danjulio/tCam/tCam-Mini/enclosure/readme.md

## tCam-Mini Enclosures

### 3D printed case
My simple 3D printed enclosure and a GoPro™ compatible mount attachment for both the Rev 2 and Rev 4 PCB tCam-Mini designs, along with the source OpenSCAD program can be found in ```tcam_mini_basic```.

The enclosure is designed to be fastened together using 4 4-40 x 3/8" metal screws (or the M3 equivalent for the rest of the world).

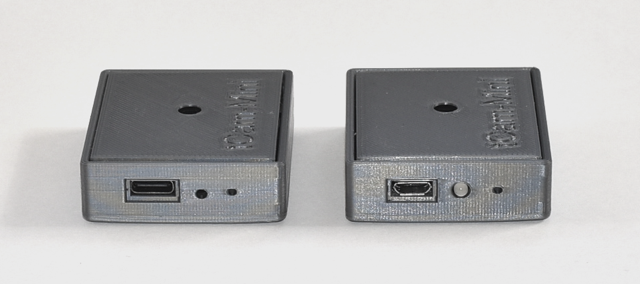
[picture p80: tCam-Mini/enclosure/pictures/tcam_mini_encl_sides.png]
Assembled units for Rev 2 and 4


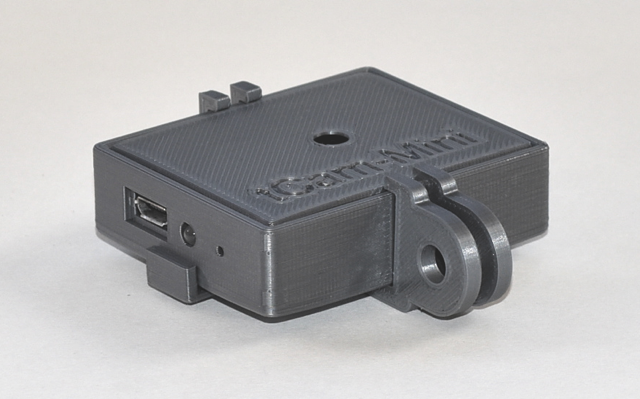
[picture p81: tCam-Mini/enclosure/pictures/tcam_mini_encl_gp_side.png]
Unit with GoPro mount


### Laser cut Front/Rear plates
A super-simple set of drawings suitable for a laser cutter in ```laser``` for a front and rear plate.  Designed to be mounted with plastic stand-offs (~8mm for the front and 5mm for the rear).  Works with either Rev 2 or Rev 4 PCBs.

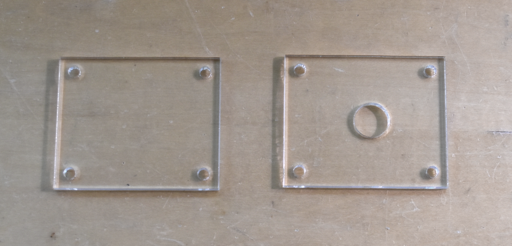
[picture p82: tCam-Mini/enclosure/pictures/tcam_mini_lasercut_pcs.png]
Cut plastic pieces


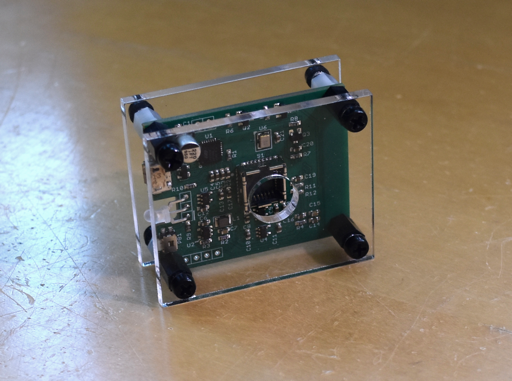
[picture p83: tCam-Mini/enclosure/pictures/tcam_mini_lasercut.png]
Cut plastic assembly


### Zeke Gustafson's 3D printed case
tCam-mini buyer Zeke Gustafson designed a case for the Rev 2 PCB and graciously shared it with me to include here.  His design file and STL files suitable for slicing for a printer can be found in ```zeke_gustafson```.

It is designed to use a 1/4"-20 square nut (McMaster 94855A247) for tripod mounting and 4x #4 thread-forming screws for assembly (McMaster 96068A105).

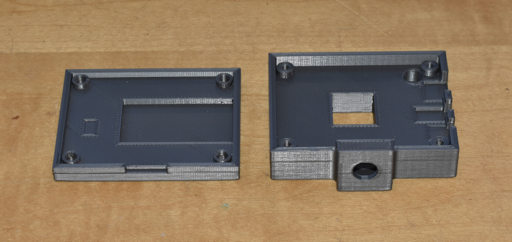
[picture p84: tCam-Mini/enclosure/pictures/zeke_enclosure_pcs.png]
Zeke Gustafson's enclosure pieces


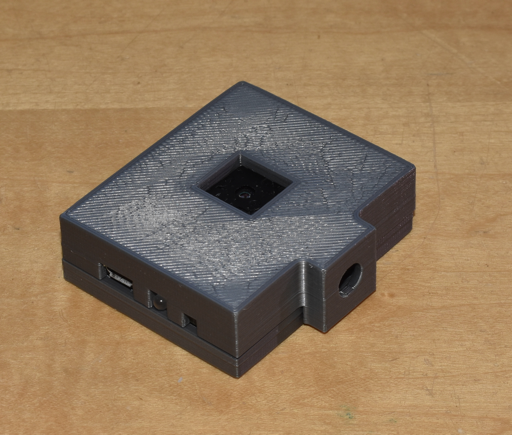
[picture p85: tCam-Mini/enclosure/pictures/zeke_enclosure.png]
Zeke Gustafson's enclosure assembly
