danjulio/tCam/tCam-Eth/hardware/tCam-Eth/documentation/4_layer_pcb_stackup.pdf

## 4-Layer Typical Stackup

Thickness: 1.6mm
Finished Outer Copper: 1oz
Inner Copper: 1oz
Inner layer Residual copper ratio: 70%

Gerber File Identification
Layer 1 Copper (PCB Top): GTL Layer 2 Copper (L2): GL2
Layer 3 Copper (L3): GL3
Layer 4 Copper (PCB Bottom): GBL

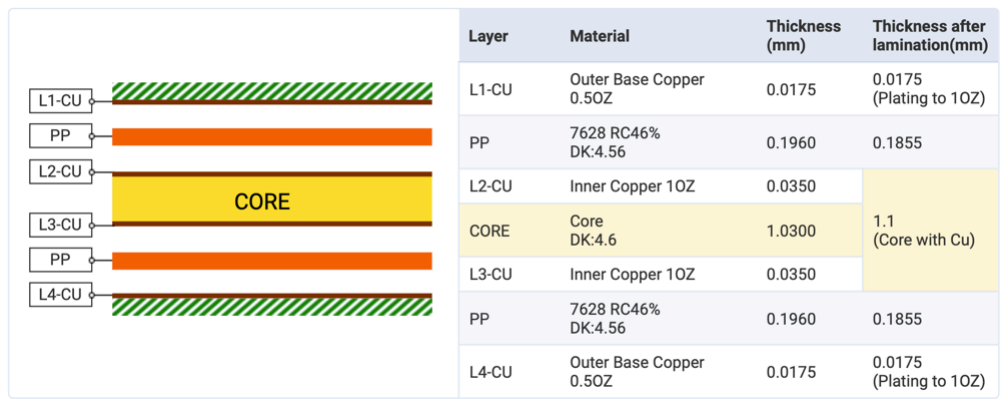
[picture p93: figure]
