danjulio/tCam/tCam-Eth/hardware/tCam-Eth/documentation/tcam_mini_eth_ref_des.jpg

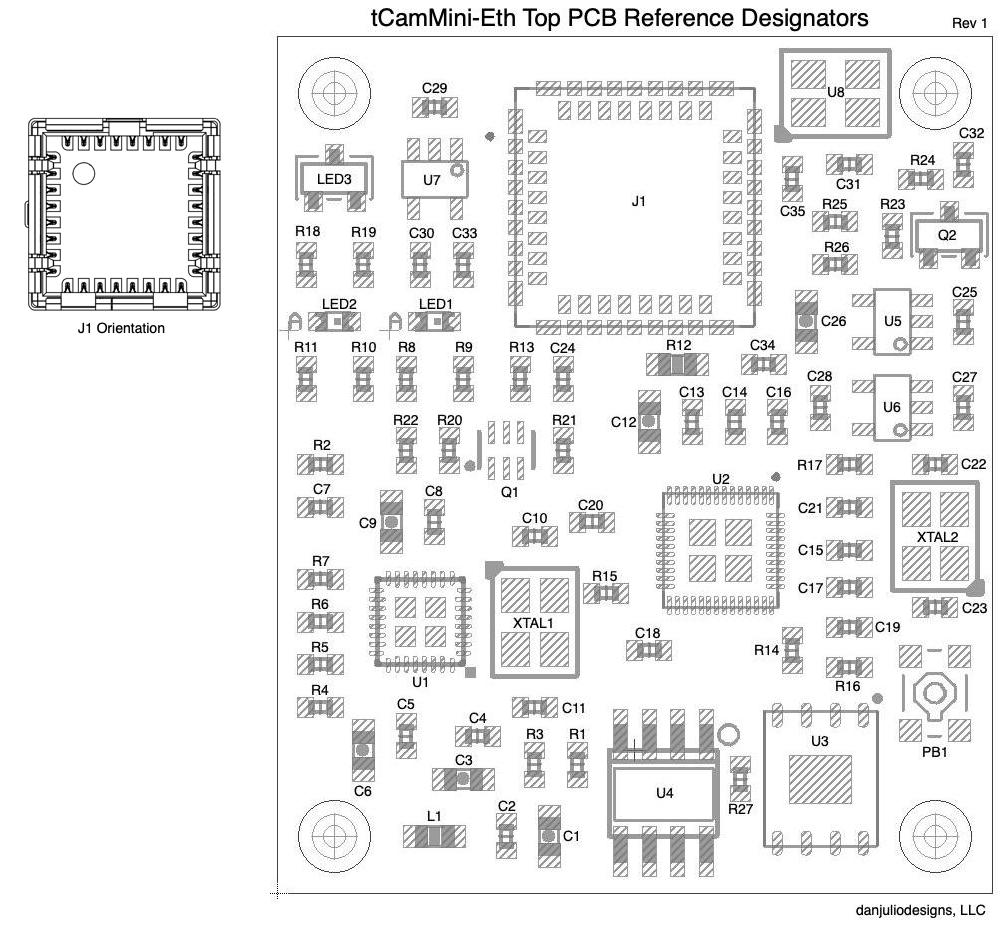
tCam-Eth/hardware/tCam-Eth/documentation/tcam_mini_eth_ref_des.jpg
