danjulio/tCam/tCam-Mini/enclosure/tcam_mini_basic/tcam_mini_basic/tcam_mini_rev4_encl.stl

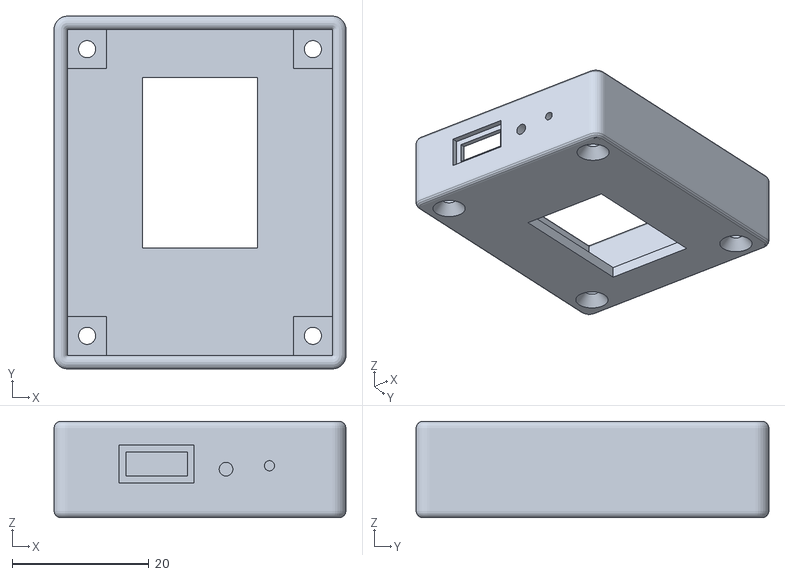
[picture p122: CAD file, 2022-11-06]
tCam-Mini/enclosure/tcam_mini_basic/tcam_mini_basic/tcam_mini_rev4_encl.stl
42.7 x 51.6 x 14.1
