danjulio/tCam/tCam/firmware/components/lvgl_esp32_drivers/lvgl_touch/touch_driver.h

/**
 * @file touch_driver.h
 */

#ifndef TOUCH_DRIVER_H
#define TOUCH_DRIVER_H

#ifdef __cplusplus
extern "C" {
#endif

#include <stdint.h>
#include <stdbool.h>
#include "lvgl/lvgl.h"


/*********************
*      DEFINES
*********************/


/**********************
 * GLOBAL PROTOTYPES
 **********************/
void touch_driver_init();
bool touch_driver_read(lv_indev_drv_t *drv, lv_indev_data_t *data);

#ifdef __cplusplus
} /* extern "C" */
#endif

#endif /* TOUCH_DRIVER_H */
