danjulio/tCam/tCam/firmware/main/cmd_task.h

/*
 * Cmd Task
 *
 * Implement the command processing module including management of the WiFi
 * interface.  Enable mDNS for device discovery.
 *
 * Copyright 2020-2022 Dan Julio
 *
 * This file is part of tCam.
 *
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
 */
#ifndef CMD_TASK_H
#define CMD_TASK_H

#include <stdbool.h>
#include <stdint.h>



//
// CMD Task Constants
//

// Commands
#define CMD_GET_STATUS  0
#define CMD_GET_IMAGE   1
#define CMD_SET_TIME    2
#define CMD_GET_WIFI    3
#define CMD_SET_WIFI    4
#define CMD_GET_CONFIG  5
#define CMD_SET_CONFIG  6
#define CMD_SET_SPOT    7
#define CMD_STREAM_ON   8
#define CMD_STREAM_OFF  9
#define CMD_TAKE_PIC    10
#define CMD_RECORD_ON   11
#define CMD_RECORD_OFF  12
#define CMD_POWEROFF    13
#define CMD_RUN_FFC     14
#define CMD_GET_FS_LIST 15
#define CMD_GET_FS_FILE 16
#define CMD_DEL_FS_OBJ  17
#define CMD_GET_LEP_CCI 18
#define CMD_SET_LEP_CCI 19
#define CMD_FW_UPD_REQ  20
#define CMD_FW_UPD_SEG  21
#define CMD_DUMP_SCREEN 22
#define CMD_NUM         23

#define CMD_UNKNOWN     999

// Command strings
#define CMD_GET_STATUS_S "get_status"
#define CMD_GET_IMAGE_S  "get_image"
#define CMD_SET_TIME_S   "set_time"
#define CMD_GET_WIFI_S   "get_wifi"
#define CMD_SET_WIFI_S   "set_wifi"
#define CMD_GET_CONFIG_S "get_config"
#define CMD_SET_CONFIG_S "set_config"
#define CMD_SET_SPOT_S   "set_spotmeter"
#define CMD_STREAM_ON_S  "stream_on"
#define CMD_STREAM_OFF_S "stream_off"
#define CMD_TAKE_PIC_S   "take_picture"
#define CMD_RECORD_ON_S  "record_on"
#define CMD_RECORD_OFF_S "record_off"
#define CMD_POWEROFF_S   "poweroff"
#define CMD_RUN_FFC_S    "run_ffc"
#define CMD_GET_FS_LIST_S "get_filesystem_list"
#define CMD_GET_FS_FILE_S "get_file"
#define CMD_DEL_FS_OBJ_S  "delete_filesystem_obj"
#define CMD_GET_LEP_CCI_S "get_lep_cci"
#define CMD_SET_LEP_CCI_S "set_lep_cci"
#define CMD_FW_UPD_REQ_S  "fw_update_request"
#define CMD_FW_UPD_SEG_S  "fw_segment"
#define CMD_DUMP_SCREEN_S "dump_screen"


// Delimiters used to wrap json strings sent over the network
#define CMD_JSON_STRING_START 0x02
#define CMD_JSON_STRING_STOP  0x03



//
// CMD Task API
//
void cmd_task();
bool cmd_connected();
int cmd_get_socket();

#endif /* CMD_TASK_H */
