danjulio/tCam/tCam/firmware/components/gui/render.c

/*
 * Renderers for lepton images, spot meter and min/max markers
 *
 * Copyright 2020, 2023 Dan Julio
 *
 * This file is part of tCam.
 *
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
 */
#include <string.h>
#include "render.h"
#include "palettes.h"
#include "gui_utilities.h"
#include "lepton_utilities.h"
#include "sys_utilities.h"


//
// Variables
//



//
// Forward declarations for internal functions
//
static void render_double_rad_data(lep_buffer_t* lep, uint16_t* img, gui_state_t* g);
static void render_double_agc_data(lep_buffer_t* lep, uint16_t* img);
static void render_interp_rad_data(lep_buffer_t* lep, uint16_t* img, gui_state_t* g);
static void render_interp_agc_data(uint16_t* buf, uint16_t* img);
static void render_min_marker(lep_buffer_t* lep, uint16_t* img);
static void render_max_marker(lep_buffer_t* lep, uint16_t* img);
static void interp_set_pixel(uint16_t src, uint16_t* img, int x, int y);
static void interp_set_outer_row(uint16_t* src, uint16_t* img, bool first_row);
static void interp_set_outer_col(uint16_t* src, uint16_t* img, bool first_col);
static void interp_set_inner(uint16_t* src, uint16_t* img);
static void draw_hline(uint16_t* img, int16_t x1, int16_t x2, int16_t y, int16_t c);
static void draw_vline(uint16_t* img, int16_t x, int16_t y1, int16_t y2, int16_t c);
static void draw_line(uint16_t* img, int16_t x1, int16_t y1, int16_t x2, int16_t y2, int16_t c);


//
// Render API
//
void render_lep_data(lep_buffer_t* lep, uint16_t* img, gui_state_t* g)
{
	if (g->display_interp_enable) {
		if (g->agc_enabled) {
			render_interp_agc_data(lep->lep_bufferP, img);
		} else {
			render_interp_rad_data(lep, img, g);
		}
	} else {
		if (g->agc_enabled) {
			render_double_agc_data(lep, img);
		} else {
			render_double_rad_data(lep, img, g);
		}
	}
}


void render_spotmeter(lep_buffer_t* lep, uint16_t* img)
{
	int16_t x1, x2, y1, y2;
	uint16_t c1, c2, r1, r2;
	uint16_t dw, dh;
	uint16_t w, h;
	
	c1 = lep->lep_telemP[LEP_TEL_SPOT_X1] * IMG_BUF_MULT_FACTOR;
	r1 = lep->lep_telemP[LEP_TEL_SPOT_Y1] * IMG_BUF_MULT_FACTOR;
	c2 = lep->lep_telemP[LEP_TEL_SPOT_X2] * IMG_BUF_MULT_FACTOR;
	r2 = lep->lep_telemP[LEP_TEL_SPOT_Y2] * IMG_BUF_MULT_FACTOR;
	
	// Spotmeter sense area dimensions
	dw = c2 - c1;
	dh = r2 - r1;
	
	// Center
	c1 = c1 + dw/2;
	r1 = r1 + dh/2;
	
	// Bounding box dimensions
	w = (dw > IMG_SPOT_MIN_SIZE) ? dw : IMG_SPOT_MIN_SIZE;
	h = (dh > IMG_SPOT_MIN_SIZE) ? dh : IMG_SPOT_MIN_SIZE;
	
	// Bounding box coordinates
	x1 = c1 - w/2;
	x2 = x1 + w;
	y1 = r1 - h/2;
	y2 = y1 + h;
	
	// Draw a white bounding box surrounded by a black bounding box for contrast
	// on all color palettes
	draw_hline(img, x1, x2, y1, 0xFFFF);
	draw_hline(img, x1, x2, y2, 0xFFFF);
	draw_vline(img, x1, y1, y2, 0xFFFF);
	draw_vline(img, x2, y1, y2, 0xFFFF);
	
	x1--;
	y1--;
	x2++;
	y2++;
	
	draw_hline(img, x1, x2, y1, 0x0000);
	draw_hline(img, x1, x2, y2, 0x0000);
	draw_vline(img, x1, y1, y2, 0x0000);
	draw_vline(img, x2, y1, y2, 0x0000);
}


void render_min_max_markers(lep_buffer_t* lep, uint16_t* img)
{
	render_min_marker(lep, img);
	render_max_marker(lep, img);
}



//
// Internal functions
//
static void render_double_rad_data(lep_buffer_t* lep, uint16_t* img, gui_state_t* g)
{
	int src_y;
	uint32_t t32;
	uint32_t diff;
	uint16_t* ptr = lep->lep_bufferP;
	uint16_t min_val, max_val;
	uint16_t t16;
	uint8_t t8;
	
	if (g->man_range_mode) {
		// Static user-set range
		if (g->rad_high_res) {
			min_val = g->man_range_min;
			max_val = g->man_range_max;
		} else {
			min_val = g->man_range_min / 10;
			max_val = g->man_range_max / 10;
		}
	} else {
		// Dynamic range from image
		min_val = lep->lep_min_val;
		max_val = lep->lep_max_val;
	}
	diff = max_val - min_val;
	
	for (src_y=0; src_y<LEP_HEIGHT; src_y++) {
		// Linearly scale then double each pixel in a source line into the destination buffer
		while (ptr < (lep->lep_bufferP + ((src_y+1)*LEP_WIDTH))) {
			if (*ptr < min_val) {
				t8 = 0;
				ptr++;
			} else {
				t32 = ((uint32_t)(*ptr++ - min_val) * 255) / diff;
				t8 = (t32 > 255) ? 255 : (uint8_t) t32;
			}
		
			t16 = PALETTE_LOOKUP(t8)
			*img++ = t16;
			*img++ = t16;
		}
		
		// Duplicate the destination buffer line
		memcpy(img, img-(2*LEP_WIDTH), 4*LEP_WIDTH);
		img += 2*LEP_WIDTH;
	}
}


static void render_double_agc_data(lep_buffer_t* lep, uint16_t* img)
{
	int src_y;
	uint16_t* ptr = lep->lep_bufferP;
	uint16_t t16;
	
	for (src_y=0; src_y<LEP_HEIGHT; src_y++) {
		// Double each pixel in a source line into the destination buffer
		while (ptr < (lep->lep_bufferP + ((src_y+1)*LEP_WIDTH))) {
			t16 = PALETTE_LOOKUP(*ptr++ & 0xFF);
			*img++ = t16;
			*img++ = t16;
		}
		
		// Duplicate the destination buffer line
		memcpy(img, img-(2*LEP_WIDTH), 4*LEP_WIDTH);
		img += 2*LEP_WIDTH;
	}
}


static void render_interp_rad_data(lep_buffer_t* lep, uint16_t* img, gui_state_t* g)
{
	uint16_t* lepP = lep->lep_bufferP;
	uint16_t* bufP = gui_render_buffer;
	uint32_t t32;
	uint16_t min_val, max_val;
	uint32_t diff;
	
	if (g->man_range_mode) {
		// Static user-set range
		if (g->rad_high_res) {
			min_val = g->man_range_min;
			max_val = g->man_range_max;
		} else {
			min_val = g->man_range_min / 10;
			max_val = g->man_range_max / 10;
		}
	} else {
		// Dynamic range from image
		min_val = lep->lep_min_val;
		max_val = lep->lep_max_val;
	}
	diff = max_val - min_val;
	 
	// Linearize the 16-bit data into 8-bits in the render buffer
	do {
		if (*lepP < min_val) {
			*bufP++ = 0;
		} else {
			t32 = ((uint32_t)(*lepP - min_val) * 255) / diff;
			*bufP++ = (t32 > 255) ? 255 : (uint8_t) t32;
		}
	} while (++lepP < (lep->lep_bufferP + LEP_WIDTH*LEP_HEIGHT));
	
	// Render 8-bit data
	render_interp_agc_data(gui_render_buffer, img);
}


static void render_interp_agc_data(uint16_t* buf, uint16_t* img)
{
	// Corner pixels
	interp_set_pixel(*buf, img, 0, 0);
	interp_set_pixel(*(buf + (LEP_WIDTH-1)), img, 2*LEP_WIDTH-1, 0);
	interp_set_pixel(*(buf + LEP_WIDTH*(LEP_HEIGHT-1)), img, 0, 2*LEP_HEIGHT-1);
	interp_set_pixel(*(buf + LEP_WIDTH*(LEP_HEIGHT-1) + (LEP_WIDTH-1)), img, 2*LEP_WIDTH-1, 2*LEP_HEIGHT-1);
	
	// Top/Bottom rows
	interp_set_outer_row(buf, img, true);
	interp_set_outer_row(buf, img, false);
	
	// Left/Right columns
	interp_set_outer_col(buf, img, true);
	interp_set_outer_col(buf, img, false);
	
	// Inner pixels
	interp_set_inner(buf, img);
}


static void render_min_marker(lep_buffer_t* lep, uint16_t* img)
{
	int16_t x1, xm, x2, y1, y2;
	
	// Compute a bounding box around the marker triangle
	x1 = lep->lep_min_x * IMG_BUF_MULT_FACTOR - (IMG_MM_MARKER_SIZE/2);
	xm = lep->lep_min_x * IMG_BUF_MULT_FACTOR;
	x2 = x1 + IMG_MM_MARKER_SIZE;
	y1 = lep->lep_min_y * IMG_BUF_MULT_FACTOR - (IMG_MM_MARKER_SIZE/2);
	y2 = y1 + IMG_MM_MARKER_SIZE;
	
	// Draw a white downward facing triangle surrounded by a black triangle for contrast
	draw_hline(img, x1, x2, y1, 0xFFFF);
	draw_line(img, x1, y1, xm, y2, 0xFFFF);
	draw_line(img, xm, y2, x2, y1, 0xFFFF);
	
	x1--;
	y1--;
	x2++;
	y2++;
	
	draw_hline(img, x1, x2, y1, 0x0000);
	draw_line(img, x1, y1, xm, y2, 0x0000);
	draw_line(img, xm, y2, x2, y1, 0x0000);
}


static void render_max_marker(lep_buffer_t* lep, uint16_t* img)
{
	int16_t x1, xm, x2, y1, y2;
	
	// Compute a bounding box around the marker triangle
	x1 = lep->lep_max_x * IMG_BUF_MULT_FACTOR - (IMG_MM_MARKER_SIZE/2);
	xm = lep->lep_max_x * IMG_BUF_MULT_FACTOR;
	x2 = x1 + IMG_MM_MARKER_SIZE;
	y1 = lep->lep_max_y * IMG_BUF_MULT_FACTOR - (IMG_MM_MARKER_SIZE/2);
	y2 = y1 + IMG_MM_MARKER_SIZE;
	
	// Draw a white upward facing triangle surrounded by a black triangle for contrast
	draw_hline(img, x1, x2, y2, 0xFFFF);
	draw_line(img, x1, y2, xm, y1, 0xFFFF);
	draw_line(img, xm, y1, x2, y2, 0xFFFF);
	
	x1--;
	y1--;
	x2++;
	y2++;
	
	draw_hline(img, x1, x2, y2, 0x0000);
	draw_line(img, x1, y2, xm, y1, 0x0000);
	draw_line(img, xm, y1, x2, y2, 0x0000);
}



/******
 *
 * Linear Interpolation Pixel Doubler
 *
 * Each source pixel is broken into 4 sub-pixels (a-d), shown below.  Each sub-
 * pixel value is based primarily by its source pixel value plus contribution from 
 * surrounding source pixels.  Four source pixels (A-D) are shown.
 *
 *      +---+---+ +---+---+
 *      | a | b | | a | b |
 *      +---A---+ +---B---+
 *      | c | d | | c | d |
 *      +---+---+ +---+---+
 *
 *      +---+---+ +---+---+
 *      | a | b | | a | b |
 *      +---C---+ +---D---+
 *      | c | d | | c | d |
 *      +---+---+ +---+---+
 * 
 * There are three cases to calculate:
 *   1. The four corners of the source array (Aa, Bb, Cc, and Dd here)
 *      - These are simply set to the value of the source pixel (A, B, C and D)
 *   2. The outer edges of the source array (Ab, Ba, Ac, Bd, Ca, Db, Dc, Dc)
 *      - The sub-pixel value is based on two source pixels (the owning pixel and its neighbor)
 *      - The owning pixel contributes more to the sub-pixel by a Scale Factor (SF)
 *      - The sub-pixel = (SF * Owning Pixel + Neighbor Pixel) / DIV
 *      - The divisor scales the sum back to 8-bits = SF + 1
 *   3. The inner sub-pixels (Ad, Bc, Cb, Da)
 *      - The sub-pixel value is based on four source pixels (the owning pixel and its neighbors)
 *      - The owning pixel contributes more to the sub-pixel by a Scale Factor (SF)
 *      - The sub-pixel = (SF * Owning Pixel + 3 Neighbor Pixels) / DIV
 *      - The divisor scales the sum back to 8-bits = SF + 3
 *
 */
 
 
/**
 * Set a single pixel in the segment buffer
 *   d contains source buffer 8-bit value
 *   img points to display buffer
 *   x, y specify position in display buffer
 */
static void interp_set_pixel(uint16_t src, uint16_t* img, int x, int y)
{
	*(img + y*2*LEP_WIDTH + x) = PALETTE_LOOKUP(src & 0xFF);
}
 

/**
 * Process either the top or bottom row in the destination buffer where each pixel
 * only depends on contributions from two source locations.
 *   src points to the lepton source buffer
 *   img points to the display buffer
 *   first_row indicates top or bottom
 */
static void interp_set_outer_row(uint16_t* src, uint16_t* img, bool first_row)
{
	int x;
	uint8_t A, B, sub_pixel;
	
	// Set the pointers to the start of the row to load
	if (first_row) {
		// Top row starting 1 pixel in (dest)
		img += 1;
	} else {
		// Bottom row starting 1 pixel in (dest)
		src += (LEP_HEIGHT-1)*LEP_WIDTH;
		img += (2*LEP_HEIGHT-1)*LEP_WIDTH*2 + 1;
	}
	
	// Inner pixels
	B = *src;
	for (x=0; x<LEP_WIDTH-1; x++) {
		A = B;
		B = *++src;
		
		// Left sub-pixel Ab (top) / Ad (bottom)
		sub_pixel = (SF_DS*A + B) / DIV_DS;
		*img++ = PALETTE_LOOKUP(sub_pixel);
		
		// Right sub-pixel Ba (top) / Bc (bottom)
		sub_pixel = (A + SF_DS*B) / DIV_DS;
		*img++ = PALETTE_LOOKUP(sub_pixel);
	}
}


/**
 * Process either the left or right column in the destination buffer where each pixel
 * only depends on contributions from two source locations.
 *   src points to the lepton source buffer
 *   img points to the display buffer
 *   first_col indicates left or right
 */
static void interp_set_outer_col(uint16_t* src, uint16_t* img, bool first_col)
{
	int y;
	uint8_t A, B, sub_pixel;
	
	// Set the pointers to the start of the column to load
	if (first_col) {
		// Left column starting 1 pixel down (dest)
		img += 2*LEP_WIDTH;
	} else {
		// Right column starting 1 pixel down (dest)
		src += LEP_WIDTH - 1;
		img += 2*LEP_WIDTH + (2*LEP_WIDTH-1);
	}
		
	// Inner pixels
	B = *src;
	for (y=0; y<LEP_HEIGHT-1; y++) {
		A = B;
		src += LEP_WIDTH;
		B = *src;
	
		// Top sub-pixel Ac (left) / Ad (right)
		sub_pixel = (SF_DS*A + B) / DIV_DS;
		*img = PALETTE_LOOKUP(sub_pixel);
		img += 2*LEP_WIDTH;
		
		// Bottom sub-pixel Ba (left) / Bb (right)
		sub_pixel = (A + SF_DS*B) / DIV_DS;
		*img = PALETTE_LOOKUP(sub_pixel);
		img += 2*LEP_WIDTH;
	}
}


/**
 * Process inner destination pixels that depend on the contribution from
 * four source pixels.
 *   src points to the lepton source buffer
 *   img points to the display buffer
 */
static void interp_set_inner(uint16_t* src, uint16_t* img)
{
	int x, y;
	uint8_t A, B, C, D, sub_pixel;
	
	// Set the destination pointer to the start of the first inner row
	img += 2*LEP_WIDTH + 1;

	// Loop over inner lines (LEP_HEIGHT-1 lines of LEP_WIDTH-1 pixels)
	for (y=0; y<LEP_HEIGHT-1; y++) {	
		// Compute all four sub-pixels in the inner section
		B = *src;
		D = *(src + LEP_WIDTH);
		for (x=0; x<LEP_WIDTH-1; x++) {
			A = B;
			C = D;
			src++;
			B = *src;
			D = *(src + LEP_WIDTH);
			
			// Lower right sub-pixel Ad
			sub_pixel = (SF_QS*A + B + C + D) / DIV_QS;
			*img = PALETTE_LOOKUP(sub_pixel);
			
			// Upper right sub-pixel Cb
			sub_pixel = (A + B + SF_QS*C + D) / DIV_QS;
			*(img + 2*LEP_WIDTH) = PALETTE_LOOKUP(sub_pixel);
			img++;
			
			// Lower left sub-pixel Bc
			sub_pixel = (A + SF_QS*B + C + D) / DIV_QS;
			*img = PALETTE_LOOKUP(sub_pixel);
			
			// Upper left sub-pixel Da
  			sub_pixel = (A + B + C + SF_QS*D) / DIV_QS;
			*(img + 2*LEP_WIDTH) = PALETTE_LOOKUP(sub_pixel);
			img++;
		}

		// Next source line, 2 dest lines down, 1-pixel in
		src++;
		img += 2*LEP_WIDTH + 2;
	}
}


static void draw_hline(uint16_t* img, int16_t x1, int16_t x2, int16_t y, int16_t c)
{
	uint16_t* imgP;
	
	if ((y < 0) || (y >= IMG_BUF_HEIGHT)) return;
	
	imgP = img + y*IMG_BUF_WIDTH + x1;
	
	while (x1 <= x2) {
		if ((x1 >= 0) && (x1 < IMG_BUF_WIDTH)) {
			*imgP = c;
		}
		imgP++;
		x1++;
	}
}


static void draw_vline(uint16_t* img, int16_t x, int16_t y1, int16_t y2, int16_t c)
{
	uint16_t* imgP;
	
	if ((x < 0) || (x >= IMG_BUF_WIDTH)) return;
	
	imgP = img + y1*IMG_BUF_WIDTH + x;
	
	while (y1 <= y2) {
		if ((y1 >= 0) && (y1 < IMG_BUF_HEIGHT)) {
			*imgP = c;
		}
		imgP += IMG_BUF_WIDTH;
		y1++;
	}
}


static void draw_line(uint16_t* img, int16_t x1, int16_t y1, int16_t x2, int16_t y2, int16_t c)
{
	int16_t dx = abs(x2 - x1);
	int16_t dy = -abs(y2 - y1);
	int16_t err = dx + dy;
	int16_t e2;
	int16_t sx = (x1 < x2) ? 1 : -1;
	int16_t sy = (y1 < y2) ? 1 : -1;
	
	for (;;) {
		if ((x1 >= 0) && (x1 < IMG_BUF_WIDTH) && (y1 >= 0) && (y1 < IMG_BUF_HEIGHT)) {
			*(img + x1 + IMG_BUF_WIDTH*y1) = c;
		}
		
		if ((x1 == x2) && (y1 == y2)) break;
		
		e2 = 2 * err;
		if (e2 >= dy) {
			err += dy;
			x1 += sx;
		}
		if (e2 <= dx) {
			err += dx;
			y1 += sy;
		}
	}
}
