danjulio/tCam/tCam/firmware/components/sys/wifi_utilities.c

/*
 * WiFi related utilities
 *
 * Contains functions to initialize the wifi interface, utility functions, and a set
 * of interface functions.  Also includes the system event handler for use by the wifi
 * system.
 *
 * Note: Currently only 1 station is allowed to connect at a time.
 *
 * Copyright 2020-2021 Dan Julio
 *
 * This file is part of tCam.
 *
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
 * You should have received a copy of the GNU General Public License
 * along with tCam.  If not, see <https://www.gnu.org/licenses/>.
 */
#include "wifi_utilities.h"
#include "ps_utilities.h"
#include "system_config.h"
#include "esp_system.h"
#include "esp_ota_ops.h"
#include "esp_log.h"
#include "esp_netif.h"
#include "freertos/FreeRTOS.h"
#include "freertos/event_groups.h"
#include "mdns.h"
#include "nvs_flash.h"
#include <string.h>



//
// Wifi Utilities local variables
//
static const char* TAG = "wifi_utilities";

// Wifi netif instance (changed each time wifi is re-started)
static esp_netif_t *wifi_netif;

// Wifi information
static char wifi_ap_ssid_array[PS_SSID_MAX_LEN+1];
static char wifi_sta_ssid_array[PS_SSID_MAX_LEN+1];
static char wifi_ap_pw_array[PS_PW_MAX_LEN+1];
static char wifi_sta_pw_array[PS_PW_MAX_LEN+1];
static wifi_info_t wifi_info = {
	wifi_ap_ssid_array,
	wifi_sta_ssid_array,
	wifi_ap_pw_array,
	wifi_sta_pw_array,
	0,
	{0, 0, 0, 0},
	{0, 0, 0, 0},
	{0, 0, 0, 0},
	{0, 0, 0, 0}
};

static const wifi_country_t def_country_info = {
	"US",
	1,
	11,
	20,
	WIFI_COUNTRY_POLICY_AUTO
};


static bool sta_connected = false; // Set when we connect to an AP so we can disconnect if we restart
static int sta_retry_num = 0;

static wifi_ap_record_t ap_info[WIFI_MAX_SCAN_LIST_SIZE];
static bool scan_in_progress = false;
static bool got_scan_done_event = false; // Set when an AP Scan is complete

// mDNS TXT records
#define NUM_SERVICE_TXT_ITEMS 3
static mdns_txt_item_t service_txt_data[NUM_SERVICE_TXT_ITEMS];
static char* txt_item_keys[NUM_SERVICE_TXT_ITEMS] = {
	"model",
	"interface",
	"version"
};



//
// WiFi Utilities Forward Declarations for internal functions
//
static bool init_esp_wifi();
static bool enable_esp_wifi_ap();
static bool enable_esp_wifi_client();
static void wifi_event_handler(void *arg, esp_event_base_t event_base, int32_t event_id, void *event_data);
static void ip_event_handler(void *arg, esp_event_base_t event_base, int32_t event_id, void *event_data);
static void start_mdns();



//
// WiFi Utilities API
//

/**
 * Power-on initialization of the WiFi system.  It is enabled based on start-up
 * information from persistent storage.  Returns false if any part of the initialization
 * fails.
 */
bool wifi_init()
{
	esp_err_t ret;
	
	// Initialize the TCP/IP stack
	ret = esp_netif_init();
	if (ret != ESP_OK) {
		ESP_LOGE(TAG, "Could not init netif (%d)", ret);
		return false;
	}
	
	// Setup the default event handlers
	ret = esp_event_loop_create_default();
	if (ret != ESP_OK) {
		ESP_LOGE(TAG, "Could not create default event loop handler (%d)", ret);
		return false;
	}
	
	ret = esp_event_handler_register(WIFI_EVENT, ESP_EVENT_ANY_ID, &wifi_event_handler, NULL);
	if (ret != ESP_OK) {
		ESP_LOGE(TAG, "Could not register wifi_event_handler (%d)", ret);
		return false;
	}
	
	ret = esp_event_handler_register(IP_EVENT, IP_EVENT_STA_GOT_IP, &ip_event_handler, NULL);
	if (ret != ESP_OK) {
		ESP_LOGE(TAG, "Could not register ip_event_handler (%d)", ret);
		return false;
	}
	
	// Initialize NVS
	ret = nvs_flash_init();
	if (ret == ESP_ERR_NVS_NO_FREE_PAGES || ret == ESP_ERR_NVS_NEW_VERSION_FOUND) {
		ret = nvs_flash_erase();
		if (ret != ESP_OK) {
			ESP_LOGI(TAG, "nvs_flash_erase failed (%d)", ret);
			return false;
		}
		ret = nvs_flash_init();
	}
	if (ret != ESP_OK) {
		ESP_LOGI(TAG, "nvs_flash_init failed (%d)", ret);
		return false;
	}
	
	// Get our wifi info
	ps_get_wifi_info(&wifi_info);
	
	// Initialize the WiFi interface
	if (init_esp_wifi()) {
		wifi_info.flags |= WIFI_INFO_FLAG_INITIALIZED;
		ESP_LOGI(TAG, "WiFi initialized");
		
		// Configure the WiFi interface if enabled
		if ((wifi_info.flags & WIFI_INFO_FLAG_STARTUP_ENABLE) != 0) {
			if ((wifi_info.flags & WIFI_INFO_FLAG_CLIENT_MODE) != 0) {
				if (enable_esp_wifi_client()) {
					wifi_info.flags |= WIFI_INFO_FLAG_ENABLED;
					ESP_LOGI(TAG, "WiFi Station starting");
				} else {
					return false;
				}
			} else {
				if (enable_esp_wifi_ap()) {
					wifi_info.flags |= WIFI_INFO_FLAG_ENABLED;
					ESP_LOGI(TAG, "WiFi AP %s enabled", wifi_info.ap_ssid);
				} else {
					return false;
				}
			}
		}
	} else {
		ESP_LOGE(TAG, "WiFi Initialization failed");
		return false;
	}
	
	// Start advertising our name and address for others to find us
	start_mdns();
	
	return true;
}


/**
 * Re-initialize the WiFi system when information such as the SSID, password or enabe-
 * state have changed.  Returns false if anything fails.
 */
bool wifi_reinit()
{
	// Disable mDNS
	mdns_free();
	
	// Attempt to disconnect from an AP if we were previously connected
	if (sta_connected) {
		ESP_LOGI(TAG, "Attempting to disconnect from AP");
		esp_wifi_disconnect();
		sta_connected = false;
	}
	
	// Shut down the old configuration
	if ((wifi_info.flags & WIFI_INFO_FLAG_ENABLED) != 0) {
		ESP_LOGI(TAG, "WiFi stopping");
		esp_wifi_stop();
		wifi_info.flags &= ~WIFI_INFO_FLAG_ENABLED;
	}
	
	// Destroy the associated esp_netif object
	esp_netif_destroy_default_wifi(wifi_netif);
	wifi_netif = NULL;
	
	if ((wifi_info.flags & WIFI_INFO_FLAG_INITIALIZED) == 0) {
		// Attempt to initialize the wifi interface again
		if (!init_esp_wifi()) {
			return false;
		}
	}
	
	// Update the wifi info because we're called when it's updated
	ps_get_wifi_info(&wifi_info);
	wifi_info.flags |= WIFI_INFO_FLAG_INITIALIZED;   // Add in the fact we're already initialized
	
	// Reconfigure the interface if enabled
	if ((wifi_info.flags & WIFI_INFO_FLAG_STARTUP_ENABLE) != 0) {
		if ((wifi_info.flags & WIFI_INFO_FLAG_CLIENT_MODE) != 0) {
			if (enable_esp_wifi_client()) {
				wifi_info.flags |= WIFI_INFO_FLAG_ENABLED;
				ESP_LOGI(TAG, "WiFi Station starting");
			} else {
				return false;
			}
		} else {
			if (enable_esp_wifi_ap()) {
				wifi_info.flags |= WIFI_INFO_FLAG_ENABLED;
				ESP_LOGI(TAG, "WiFi AP %s enabled", wifi_info.ap_ssid);
			} else {
				return false;
			}
		}
	}
	
	// Nothing should be connected now
	wifi_info.flags &= ~WIFI_INFO_FLAG_CONNECTED;
	
	// Re-enable mDNS
	start_mdns();
	
	return true;
}


/**
 * Setup for and start an AP scan
 *   - Disables WiFi and disconnects from an AP if currently connected
 */
bool wifi_setup_scan()
{
	esp_err_t ret;
	wifi_config_t wifi_config = {
		.sta = {
			.ssid[0] = 0,
			.password[0] = 0,
			.scan_method = WIFI_ALL_CHANNEL_SCAN,
			.bssid_set = 0,
			.channel = 0,
			.listen_interval = 0,
			.sort_method = WIFI_CONNECT_AP_BY_SIGNAL			
		}
	};
	
	got_scan_done_event = false;
	
	// Disable mDNS
	mdns_free();
	
	// Attempt to disconnect from an AP if we were previously connected
	if (sta_connected) {
		ESP_LOGI(TAG, "Attempting to disconnect from AP");
		esp_wifi_disconnect();
		sta_connected = false;
	}
	
	// Shut down the old configuration
	if ((wifi_info.flags & WIFI_INFO_FLAG_ENABLED) != 0) {
		ESP_LOGI(TAG, "WiFi stopping");
		esp_wifi_stop();
		wifi_info.flags &= ~WIFI_INFO_FLAG_ENABLED;
	}

	if ((wifi_info.flags & WIFI_INFO_FLAG_INITIALIZED) == 0) {
		// Attempt to initialize the wifi interface again
		ESP_LOGI(TAG, "Re-init WiFi");
		if (!init_esp_wifi()) {
			return false;
		}
	}
	
	// Configure into STA mode and start a scan
    ret = esp_wifi_set_mode(WIFI_MODE_STA);
    if (ret != ESP_OK) {
    	ESP_LOGE(TAG, "Could not set Station mode for scan (%d)", ret);
    	return false;
    }
    
    ret = esp_wifi_set_config(ESP_IF_WIFI_STA, &wifi_config);
    if (ret != ESP_OK) {
    	ESP_LOGE(TAG, "Could not set Station configuration for scan (%d)", ret);
    	return false;
    }
    
    ret = esp_wifi_start();
    if (ret != ESP_OK) {
    	ESP_LOGE(TAG, "Could not start Station for scan (%d)", ret);
    	return false;
    }
    
    scan_in_progress = true;
    ret = esp_wifi_scan_start(NULL, false);
    if (ret != ESP_OK) {
    	ESP_LOGE(TAG, "Could not start scan (%d)", ret);
    	scan_in_progress = false;
    	return false;
    }
    wifi_info.flags |= WIFI_INFO_FLAG_ENABLED;
    
    ESP_LOGI(TAG, "Start scan");
    
    return true;
}


/**
 * Stop a scan if it is in progress
 */
void wifi_stop_scan()
{
	// Since this should only be called if we've started a scan, don't sweat the return
	// code
	(void) esp_wifi_scan_stop();
	scan_in_progress = false;
	got_scan_done_event = false;
}


/**
 * Return connected to client status
 */
bool wifi_is_connected()
{
	return ((wifi_info.flags & WIFI_INFO_FLAG_CONNECTED) != 0);
}


/**
 * Return scan completion status
 */
bool wifi_scan_is_complete()
{
	return got_scan_done_event;
}


/**
 * Return current WiFi configuration and state
 */
wifi_info_t* wifi_get_info()
{
	return &wifi_info;
}


/**
 * Return a pointer to an array of wifi_ap_record_t structures
 */
int wifi_get_scan_records(wifi_ap_record_t **ap)
{
	esp_err_t ret;
	uint16_t number = WIFI_MAX_SCAN_LIST_SIZE;
	uint16_t ap_count = 0;
	
	*ap = &ap_info[0];
	
	if (got_scan_done_event) {
    	memset(ap_info, 0, sizeof(ap_info));
    	ret = esp_wifi_scan_get_ap_records(&number, ap_info);
    	if (ret != ESP_OK) {
			ESP_LOGE(TAG, "Could not get ap_info (%d)", ret);
			return 0;
		}
		
    	ret = esp_wifi_scan_get_ap_num(&ap_count);
    	if (ret != ESP_OK) {
			ESP_LOGE(TAG, "Could not get ap_num (%d)", ret);
			return 0;
		}
		
		ESP_LOGI(TAG, "Total APs found = %u", ap_count);
		return ap_count;
	} else {
		return 0;
	}
}


//
// WiFi Utilities internal functions
//

/**
 * Initialize the WiFi interface resources
 */
static bool init_esp_wifi()
{
	esp_err_t ret;
	wifi_init_config_t cfg = WIFI_INIT_CONFIG_DEFAULT();
	
	ret = esp_wifi_init(&cfg);
	if (ret != ESP_OK) {
		ESP_LOGE(TAG, "Could not allocate wifi resources (%d)", ret);
		return false;
	}
	
	// We don't need the NVS configuration storage for the WiFi configuration since we
	// are managing persistent storage ourselves
	ret = esp_wifi_set_storage(WIFI_STORAGE_RAM);
	if (ret != ESP_OK) {
		ESP_LOGE(TAG, "Could not set RAM storage for configuration (%d)", ret);
		return false;
	}
		
	// Setup WiFi country restrictions to US/AUTO
	ret = esp_wifi_set_country(&def_country_info);
	if (ret != ESP_OK) {
		ESP_LOGE(TAG, "Could not set default country configuration - %x", ret);
		return false;
	}
	
	return true;
}


/**
 * Enable this device as a Soft AP
 */
static bool enable_esp_wifi_ap()
{
	esp_err_t ret;
	int i;
	
	// Create the esp_netif object
	wifi_netif = esp_netif_create_default_wifi_ap();
	
	// Enable the AP
	wifi_config_t wifi_config = {
        .ap = {
            .ssid_len = strlen(wifi_info.ap_ssid),
            .max_connection = 1,
            .authmode = WIFI_AUTH_WPA_WPA2_PSK
        }
    };
    strcpy((char*) wifi_config.ap.ssid, wifi_info.ap_ssid);
    strcpy((char*) wifi_config.ap.password, wifi_info.ap_pw);
    if (strlen(wifi_info.ap_pw) == 0) {
        wifi_config.ap.authmode = WIFI_AUTH_OPEN;
    }
    
    ret = esp_wifi_set_mode(WIFI_MODE_AP);
    if (ret != ESP_OK) {
    	ESP_LOGE(TAG, "Could not set Soft AP mode (%d)", ret);
    	return false;
    }
    
    ret = esp_wifi_set_config(ESP_IF_WIFI_AP, &wifi_config);
    if (ret != ESP_OK) {
    	ESP_LOGE(TAG, "Could not set Soft AP configuration (%d)", ret);
    	return false;
    }
    
    ret = esp_wifi_start();
    if (ret != ESP_OK) {
    	ESP_LOGE(TAG, "Could not start Soft AP (%d)", ret);
    	return false;
    }
    
    // For now, since we are using the default IP address, copy it to the current here
    for (i=0; i<4; i++) {
    	wifi_info.cur_ip_addr[i] = wifi_info.ap_ip_addr[i];
    }
    	
    return true;
}


/**
 * Enable this device as a Client
 */
static bool enable_esp_wifi_client()
{
	esp_err_t ret;
	esp_netif_ip_info_t ipInfo;
	
	// Configure the IP address mechanism
	if ((wifi_info.flags & WIFI_INFO_FLAG_CL_STATIC_IP) != 0) {
		// Static IP
		//
		// Create the esp_netif object
		wifi_netif = esp_netif_create_default_wifi_sta();
		
		// Stop the DHCP client
		ret = esp_netif_dhcpc_stop(wifi_netif);
		if ((ret != ESP_OK) && (ret != ESP_ERR_ESP_NETIF_DHCP_ALREADY_STOPPED)) {
    		ESP_LOGE(TAG, "Stop Station DHCP returned %d", ret);
    		return false;
    	}
    	
		ipInfo.ip.addr = wifi_info.sta_ip_addr[3] |
						 (wifi_info.sta_ip_addr[2] << 8) |
						 (wifi_info.sta_ip_addr[1] << 16) |
						 (wifi_info.sta_ip_addr[0] << 24);
  		ipInfo.gw.addr = esp_netif_ip4_makeu32(0, 0, 0, 0);
  		ipInfo.netmask.addr = wifi_info.sta_netmask[3] |
						     (wifi_info.sta_netmask[2] << 8) |
						     (wifi_info.sta_netmask[1] << 16) |
						     (wifi_info.sta_netmask[0] << 24);
  		ret = esp_netif_set_ip_info(wifi_netif, &ipInfo);
		if (ret != ESP_OK) {
			ESP_LOGE(TAG, "Set IP info returned %d", ret);
		}
	} else {
		// DHCP served address
		//
		// Create the esp_netif object
		wifi_netif = esp_netif_create_default_wifi_sta();
		
		ret = esp_netif_dhcpc_start(wifi_netif);
		if (ret != ESP_OK) {
    		ESP_LOGE(TAG, "Start Station DHCP returned %d", ret);
    		return false;
    	}
	}
	
	// Enable the Client
	wifi_config_t wifi_config = {
		.sta = {
			.scan_method = WIFI_FAST_SCAN,
			.bssid_set = 0,
			.channel = 0,
			.listen_interval = 0,
			.sort_method = WIFI_CONNECT_AP_BY_SIGNAL			
		}
	};	
    strcpy((char*) wifi_config.sta.ssid, wifi_info.sta_ssid);
    if (strlen(wifi_info.sta_pw) == 0) {
        strcpy((char*) wifi_config.sta.password, "");
    } else {
    	strcpy((char*) wifi_config.sta.password, wifi_info.sta_pw);
    }
    
    ret = esp_wifi_set_mode(WIFI_MODE_STA);
    if (ret != ESP_OK) {
    	ESP_LOGE(TAG, "Could not set Station mode (%d)", ret);
    	return false;
    }
    
    ret = esp_wifi_set_config(ESP_IF_WIFI_STA, &wifi_config);
    if (ret != ESP_OK) {
    	ESP_LOGE(TAG, "Could not set Station configuration (%d)", ret);
    	return false;
    }
    
    ret = esp_wifi_start();
    if (ret != ESP_OK) {
    	ESP_LOGE(TAG, "Could not start Station (%d)", ret);
    	return false;
    }
    
    return true;
}


/**
 * Handle system events that we care about from the WiFi task
 */
static void wifi_event_handler(void *arg, esp_event_base_t event_base, int32_t event_id, void *event_data)
{
	wifi_event_ap_staconnected_t *con_event;
	wifi_event_ap_stadisconnected_t *dis_event;
	
	switch (event_id) {
		case WIFI_EVENT_AP_STACONNECTED:
			con_event = (wifi_event_ap_staconnected_t *) event_data;
			wifi_info.flags |= WIFI_INFO_FLAG_CONNECTED;
			ESP_LOGI(TAG, "Station:"MACSTR" join, AID=%d", MAC2STR(con_event->mac), con_event->aid);
			break;
		
		case WIFI_EVENT_AP_STADISCONNECTED:
			dis_event = (wifi_event_ap_stadisconnected_t *) event_data;
			wifi_info.flags &= ~WIFI_INFO_FLAG_CONNECTED;
			ESP_LOGI(TAG, "Station:"MACSTR" leave, AID=%d", MAC2STR(dis_event->mac), dis_event->aid);
			break;
			
		case WIFI_EVENT_STA_START:
			if (scan_in_progress) {
				ESP_LOGI(TAG, "Station started for scan");
			} else {
				ESP_LOGI(TAG, "Station started, trying to connect to %s", wifi_info.sta_ssid);
				esp_wifi_connect();
			}
			sta_retry_num = 0;
        	break;
        
        case WIFI_EVENT_STA_STOP:
        	ESP_LOGI(TAG, "Station stopped");
        	break;
        	
        case WIFI_EVENT_STA_CONNECTED:
        	ESP_LOGI(TAG, "Station connected");
        	break;
        	
        case WIFI_EVENT_STA_DISCONNECTED:
        	wifi_info.flags &= ~WIFI_INFO_FLAG_CONNECTED;
        	if (!scan_in_progress) {
        		if (sta_retry_num > WIFI_FAST_RECONNECT_ATTEMPTS) {
        			vTaskDelay(pdMS_TO_TICKS(1000));
        		} else {
        			++sta_retry_num;
        		}
                esp_wifi_connect();
                ESP_LOGI(TAG, "Retry connection to %s", wifi_info.sta_ssid);
            }
        	break;
        	
        case WIFI_EVENT_SCAN_DONE:
        	ESP_LOGI(TAG, "Scan done");
        	scan_in_progress = false;
        	got_scan_done_event = true;
        	break;
	}
}


/**
 * Handle events from the TCP/IP stack
 */
static void ip_event_handler(void *arg, esp_event_base_t event_base, int32_t event_id, void *event_data)
{
	ip_event_got_ip_t *event = (ip_event_got_ip_t *) event_data;
	const esp_netif_ip_info_t *ip_info = &event->ip_info;
	
	wifi_info.flags |= WIFI_INFO_FLAG_CONNECTED;
    sta_connected = true;
    sta_retry_num = 0;
	
	ESP_LOGI(TAG, "Got IP Address: " IPSTR, IP2STR(&ip_info->ip));
	
    wifi_info.cur_ip_addr[3] = ip_info->ip.addr & 0xFF;
    wifi_info.cur_ip_addr[2] = (ip_info->ip.addr >> 8) & 0xFF;
    wifi_info.cur_ip_addr[1] = (ip_info->ip.addr >> 16) & 0xFF;
	wifi_info.cur_ip_addr[0] = (ip_info->ip.addr >> 24) & 0xFF;
}


/**
 * Start the mDNS responder
 */
static void start_mdns()
{
	char model_type[2];     // Camera Model number "N"
	char txt_if_type[5];    // "WiFi"
	const esp_app_desc_t* app_desc;
	esp_err_t ret;
	wifi_info_t* wifi_infoP;
	
	// Attempt to initialize mDNS
	ret = mdns_init();
	if (ret != ESP_OK) {
		ESP_LOGE(TAG, "Could not initialize mDNS (%d)", ret);
		return;
	}
	
	// Set our hostname
	wifi_infoP = wifi_get_info();
	ret = mdns_hostname_set(wifi_infoP->ap_ssid);
	if (ret != ESP_OK) {
		ESP_LOGE(TAG, "Could not set mDNS hostname %s (%d)", wifi_infoP->ap_ssid, ret);
		return;
	}
	
	// Get dynamic info for TXT records
	app_desc = esp_ota_get_app_description();  // Get version info
	model_type[0] = '0' + CAMERA_MODEL_NUM;
	model_type[1] = 0;
	strcpy(txt_if_type, "WiFi");
	
	service_txt_data[0].key = txt_item_keys[0];
	service_txt_data[0].value = model_type;
	service_txt_data[1].key = txt_item_keys[1];
	service_txt_data[1].value = txt_if_type;
	service_txt_data[2].key = txt_item_keys[2];
	service_txt_data[2].value = app_desc->version;
	
	// Initialize service
	ret = mdns_service_add(NULL, "_tcam-socket", "_tcp", CMD_PORT, service_txt_data, NUM_SERVICE_TXT_ITEMS);
	if (ret != ESP_OK) {
		ESP_LOGE(TAG, "Could not initialize mDNS service (%d)", ret);
		return;
	}
	
	ESP_LOGI(TAG, "mDNS started");
}
