danjulio/tCam/tCam/firmware/components/gcore/time_utilities.c

/*
 * Time related utilities
 *
 * Contains functions to interface the RTC to the system timekeeping
 * capabilities and provide application access to the system time.
 *
 * Copyright 2020-2021 Dan Julio
 *
 * This file is part of tCam.
 *
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
 */
#include "time_utilities.h"
#include "esp_system.h"
#include "esp_log.h"
#include <stdlib.h>
#include <time.h>
#include <sys/time.h>


//
// Time Utilities Constants
//

// Leap year calulator expects year argument as years offset from 1970
#define LEAP_YEAR(Y)     ( ((1970+(Y))>0) && !((1970+(Y))%4) && ( ((1970+(Y))%100) || !((1970+(Y))%400) ) )

// Useful time constants
#define SECS_PER_MIN  ((time_t)(60UL))
#define SECS_PER_HOUR ((time_t)(3600UL))
#define SECS_PER_DAY  ((time_t)(SECS_PER_HOUR * 24UL))
#define DAYS_PER_WEEK ((time_t)(7UL))
#define SECS_PER_WEEK ((time_t)(SECS_PER_DAY * DAYS_PER_WEEK))
#define SECS_PER_YEAR ((time_t)(SECS_PER_DAY * 365UL)) // TODO: ought to handle leap years
#define SECS_YR_2000  ((time_t)(946684800UL)) // the time at the start of y2k

#define MSECS_PER_DAY (SECS_PER_DAY * 1000UL)


// Minimum epoch time (12:00:00 AM Jan 1 2000)
#define MIN_EPOCH_TIME 946684800



//
// Time Utilities date related strings (related to tmElements)
//
static const char* day_strings[] = {
	"Err",
	"Sun",
	"Mon",
	"Tue",
	"Wed",
	"Thu",
	"Fri",
	"Sat"
};

static const char* mon_strings[] = {
	"Err",
	"Jan",
	"Feb",
	"Mar",
	"Apr",
	"May",
	"Jun",
	"Jul",
	"Aug",
	"Sep",
	"Oct",
	"Nov",
	"Dec"
};

// API starts months from 1, this array starts from 0
static const uint8_t monthDays[] =
	{31,28,31,30,31,30,31,31,30,31,30,31};


//
// Time Utilities Variables
//
static const char* TAG = "time_utilities";


 
//
// Time Utilities API
//

/**
 * Initialize system time from the RTC
 */
void time_init()
{
	char buf[26];
	tmElements_t te;
	struct timeval tv;
	time_t secs;
	
	// Set the system time from the RTC
	secs = rtc_get_time_secs();
	if (secs < MIN_EPOCH_TIME) {
		secs = MIN_EPOCH_TIME;
		(void) rtc_set_time_secs(secs);
	}
	tv.tv_sec = secs;
	tv.tv_usec = 0;
	settimeofday((const struct timeval *) &tv, NULL);
	
	// Diagnostic display of time
	time_get(&te);
	time_get_disp_string(te, buf);
	ESP_LOGI(TAG, "Initial RTC time: %s  (epoch secs: %d)", buf, (uint32_t) secs);
}


/**
 * Set the system time and update the RTC
 */
void time_set(tmElements_t te)
{
	struct timeval tv;
	time_t secs;
	
	// Attempt to set the RTC
	if (!rtc_write_time(te)) {
		ESP_LOGE(TAG, "Update RTC failed");
	}
	
	// Set the system time
	secs = rtc_makeTime(te);
	tv.tv_sec = secs;
	tv.tv_usec = 0;
	settimeofday((const struct timeval *) &tv, NULL);
}


/**
 * Get the system time
 */
void time_get(tmElements_t* te)
{
	time_t now;
	struct timeval tv;
	struct tm timeinfo;
	
	// Get the time and convert into our simplified tmElements format
	(void) gettimeofday(&tv, NULL);
	//time(&now);
	now = tv.tv_sec;
    localtime_r(&now, &timeinfo);  // Get the unix formatted timeinfo
    mktime(&timeinfo);             // Fill in the DOW and DOY fields
    te->Millisecond = (uint16_t) (tv.tv_usec / 1000);
    te->Second = (uint8_t) timeinfo.tm_sec;
    te->Minute = (uint8_t) timeinfo.tm_min;
    te->Hour = (uint8_t) timeinfo.tm_hour;
    te->Wday = (uint8_t) timeinfo.tm_wday + 1; // Sunday is 1 in our tmElements structure
    te->Day = (uint8_t) timeinfo.tm_mday;
    te->Month = (uint8_t) timeinfo.tm_mon + 1; // January is 1 in our tmElements structure
    te->Year = (uint8_t) timeinfo.tm_year - 70; // tmElements starts at 1970
}


/**
 * Return true if the system time (in seconds) has changed from the last time
 * this function returned true. Each calling task must maintain its own prev_time
 * variable (it can initialize it to 0).  Set te to NULL if you don't need the time.
 */
bool time_changed(tmElements_t* te, time_t* prev_time)
{
	time_t now;
	struct tm timeinfo;
	
	// Get the time and check if it is different
	time(&now);
	if (now != *prev_time) {
		*prev_time = now;
		
		if (te != NULL) {
			// convert time into our simplified tmElements format
    		localtime_r(&now, &timeinfo);  // Get the unix formatted timeinfo
    		mktime(&timeinfo);             // Fill in the DOW and DOY fields
    		te->Millisecond = 0;
    		te->Second = (uint8_t) timeinfo.tm_sec;
    		te->Minute = (uint8_t) timeinfo.tm_min;
    		te->Hour = (uint8_t) timeinfo.tm_hour;
    		te->Wday = (uint8_t) timeinfo.tm_wday + 1; // Sunday is 1 in our tmElements structure
    		te->Day = (uint8_t) timeinfo.tm_mday;
    		te->Month = (uint8_t) timeinfo.tm_mon + 1; // January is 1 in our tmElements structure
    		te->Year = (uint8_t) timeinfo.tm_year - 70; // tmElements starts at 1970
    	}
    	
    	return true;
    } else {
    	return false;
    }
}


/**
 * Load buf with a time & date string for display.
 *
 *   "DOW MON DAY HH:MM:SS YEAR"
 *
 * buf must be at least 26 bytes long (to include null termination).
 */
void time_get_disp_string(tmElements_t te, char* buf)
{
	// Validate te to prevent illegal accesses to the constant string buffers
	if (te.Wday > 7) te.Wday = 0;
	if (te.Month > 12) te.Month = 0;
	
	// Build up the string
	sprintf(buf,"%s %s %2d %2d:%02d:%02d %4d", 
		day_strings[te.Wday],
		mon_strings[te.Month],
		te.Day,
		te.Hour,
		te.Minute,
		te.Second,
		te.Year + 1970);
}


/**
 * Load buf with a short time or date string with no spaces.  Useful for constructing
 * a file or directory name.
 *
 *   "YY_MM_DD or HH_MM_SS"
 *
 * buf must be at least 18 bytes long (to include null termination)
 */
void time_get_file_date_string(tmElements_t te, char* buf)
{
	// Always assume we are running post 2000
	te.Year = tmYearToY2k(te.Year);
	
	// Build up the string
	sprintf(buf, "%02d_%02d_%02d", te.Year, te.Month, te.Day);
}


void time_get_file_time_string(tmElements_t te, char* buf)
{
	// Build up the string
	sprintf(buf, "%d_%02d_%02d", te.Hour, te.Minute, te.Second);
}


/**
 * Load buf with full American date format: "MM/DD/YY" with YY from 2000
 */
void time_get_full_date_string(tmElements_t te, char* buf)
{
	// Always assume we are running post 2000
	te.Year = tmYearToY2k(te.Year);
	
	// Build up the string
	sprintf(buf, "%d/%d/%02d", te.Month, te.Day, te.Year);
}


/**
 * Load buf with full time format: "HH:MM:SS.mmm"
 * Useful for constructing status, metadata or video_info packets. 
 */
void time_get_full_time_string(tmElements_t te, char* buf)
{
	// Build up the string
	sprintf(buf, "%d:%02d:%02d.%d", te.Hour, te.Minute, te.Second, te.Millisecond);
}


/**
 * Load buf with hours & minutes string for display
 *
 *   "HH:MM"
 *
 * buf must be at least 6 bytes long (to include null termination)
 */
void time_get_hhmm_string(tmElements_t te, char* buf)
{
	sprintf(buf, "%02d:%02d", te.Hour, te.Minute);
}
 

/**
 * Fill in a tmElements structure from time and date strings with the format
 *   time: "HH:MM:SS.msec"
 *   date: "MM/DD/YY"          year assumed to be post 2000
 */
void time_get_time_from_strings(tmElements_t* te, char* timespec, char* datespec)
{
	char c;
	int days;
	int i = 0;
	
	// Initialize the tmElements structure
	te->Millisecond = 0;
	te->Second = 0;
	te->Minute = 0;
	te->Hour = 0;
	te->Wday = 0;
	te->Day = 0;
	te->Month = 0;
	te->Year = 0;
	
	// Parse the time string
	c = *timespec++;
	while (c != 0) {
		if ((c >= '0') && (c <= '9')) {
			switch (i) {
				case 0:
					te->Hour = (te->Hour * 10) + (c - '0');
					break;
				case 1:
					te->Minute = (te->Minute * 10) + (c - '0');
					break;
				case 2:
					te->Second = (te->Second * 10) + (c - '0');
					break;
				case 3:
					te->Millisecond = (te->Millisecond * 10) + (c - '0');
					break;
			}
		} else if (c == ':') {
			i += 1;
		} else if (c == '.') {
			i = 3;
		}
		c = *timespec++;
	}
	
	// Parse the date string
	c = *datespec++;
	i = 0;
	while (c != 0) {
		if ((c >= '0') && (c <= '9')) {
			switch (i) {
				case 0:
					te->Month = (te->Month * 10) + (c - '0');
					break;
				case 1:
					te->Day = (te->Day * 10) + (c - '0');
					break;
				case 2:
					te->Year = (te->Year * 10) + (c - '0');
					break;
			}
		} else if (c == '/') {
			i += 1;
		}
		c = *datespec++;
	}
	
	// Fix-up the year to be post 1970
	te->Year += 30;
	
	// Create the Wday value (based on the fast breakTime algorithm using the number
	// of days in the date)
	days = (te->Year + 1970) * 365;
	for (i = 0; i < te->Year; i++) {
		if (LEAP_YEAR(i)) {
			days += 1;   // add extra days for leap years
		}
	}
	// Add days for this year, months start from 1
	for (i = 1; i < te->Month; i++) {
		if ( (i == 2) && LEAP_YEAR(te->Year)) { 
			days += 29;
		} else {
			days += monthDays[i-1];  //monthDay array starts from 0
		}
	}
	days += te->Day - 1;  // Day starts from 1

	// Finally compute Wday (Sunday is day 1)
	te->Wday = ((days + 4) % 7) + 1;
}


/**
 * Convert a video playback timestamp to the form 
 *   if H > 0  -> H:MM:SS 
 *   else      ->   MM:SS
 * 
 * buf must be adequately sized.
 */
void time_get_disp_string_from_msec(uint32_t ms, char* buf)
{
	int s, m, h;
	
	// Convert the ms timestamp into time components
	s = ms / 1000;
	if ((ms % 1000) >= 500) {
		s = s + 1;
	}
	h = s / SECS_PER_HOUR;
	s = s - (h * SECS_PER_HOUR);
	m = s / SECS_PER_MIN;
	s = s - (m * SECS_PER_MIN);
	
	// Build up the string
	if (h == 0) {
		sprintf(buf, "%02d:%02d", m, s);
	} else {
		sprintf(buf, "%d:%02d:%02d", h, m, s);
	}
}


/**
 * Return milliseconds since the epoch for the given time
 */
uint64_t time_get_millis(tmElements_t te)
{
	int i;
	uint64_t msec;

	// msec from 1970 till 1 jan 00:00:00 of the given year
	msec = te.Year*(MSECS_PER_DAY * 365);
	for (i = 0; i < te.Year; i++) {
		if (LEAP_YEAR(i)) {
			msec +=  MSECS_PER_DAY;   // add extra days for leap years
		}
	}
  
	// add days for this year, months start from 1
	for (i = 1; i < te.Month; i++) {
		if ( (i == 2) && LEAP_YEAR(te.Year)) { 
			msec += SECS_PER_DAY * 29;
		} else {
			msec += SECS_PER_DAY * monthDays[i-1];  //monthDay array starts from 0
		}
	}
	msec += (te.Day-1) * SECS_PER_DAY * 1000UL;
	msec += te.Hour * SECS_PER_HOUR * 1000UL;
	msec += te.Minute * SECS_PER_MIN * 1000UL;
	msec += te.Second * 1000UL;
	msec += te.Millisecond;
	
	return msec; 
}
