danjulio/tCam/tCam/firmware/main/gui_task.c

/*
 * GUI Task
 *
 * Contains functions to initialize the LittleVGL GUI system and a task
 * to evaluate its display related sub-tasks.  The GUI Task is responsible
 * for all access (updating) of the GUI managed by LittleVGL.
 *
 * Copyright 2020-2022 Dan Julio
 *
 * This file is part of tCam.
 *
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
 */
#include "gui_task.h"
#include "app_task.h"
#include "lep_task.h"
#include "rsp_task.h"
#include "freertos/FreeRTOS.h"
#include "freertos/task.h"
#include "esp_system.h"
#include "esp_log.h"
#include "esp_freertos_hooks.h"
#include "system_config.h"
#include "disp_spi.h"
#include "disp_driver.h"
#include "touch_driver.h"
#include "sys_utilities.h"
#include "gui_screen_main.h"
#include "gui_screen_settings.h"
#include "gui_screen_num_entry.h"
#include "gui_screen_emissivity.h"
#include "gui_screen_info.h"
#include "gui_screen_network.h"
#include "gui_screen_time.h"
#include "gui_screen_wifi.h"
#include "gui_screen_view.h"
#include "gui_screen_browse.h"
#include "gui_screen_update.h"
#include "gui_utilities.h"
#ifdef SYS_SCREENDUMP_ENABLE
#include "rsp_task.h"
#include "mem_fb.h"
#endif



//
// GUI Task internal constants
//

// LVGL sub-task indicies
#define LVGL_ST_EVENT       0
#define LVGL_ST_MESSAGEBOX  1
#define LVGL_ST_NUM         2


//
// GUI Task variables
//
static const char* TAG = "gui_task";

// Dual display update buffers to allow DMA/SPI transfer of one while the other is updated
static lv_color_t lvgl_disp_buf1[LVGL_DISP_BUF_SIZE];
static lv_color_t lvgl_disp_buf2[LVGL_DISP_BUF_SIZE];
static lv_disp_buf_t lvgl_disp_buf;

// Display driver
static lv_disp_drv_t lvgl_disp_drv;

// Touchscreen driver
static lv_indev_drv_t lvgl_indev_drv;

// Screen object array and current screen index
static lv_obj_t* gui_screens[GUI_NUM_SCREENS];
static int gui_cur_screen_index = -1;

// LVGL sub-task array
static lv_task_t* lvgl_tasks[LVGL_ST_NUM];

// FPS averaging array (mSec between )
static int64_t prev_fps_sample_time;
static int fps_array_index;
static int fps_delta_msec_array[GUI_NUM_FPS_SAMPLES];

// Filename to display for recorded images
static char record_filename[20];

// Request to display message box
static bool req_message_box;
static bool fw_req_upd_message_box = false;

// Playback timestamp destined for gui_screen_view
static uint32_t video_ts;


//
// GUI Task internal function forward declarations
//
static bool gui_lvgl_init();
static void gui_screen_init();
static void gui_add_subtasks();
static void gui_task_event_handler_task(lv_task_t * task);
static void gui_task_messagebox_handler_task(lv_task_t * task);
static void IRAM_ATTR lv_tick_callback();
static void gui_init_fps();
static void gui_update_fps();
#ifdef SYS_SCREENDUMP_ENABLE
static void gui_do_screendump();
#endif



//
// GUI Task API
//

/**
 * GUI Task - Executes all GUI/display related activities via LittleVGL objects
 * and LittleVGL sub-tasks evaluated by lv_task_handler.  Communication with other
 * tasks is handled in this routine although various LVGL callbacks and event code
 * may call routines in other modules to get or set state.
 */
void gui_task()
{
	ESP_LOGI(TAG, "Start task");

	// Initialize
	if (!gui_lvgl_init()) {
		vTaskDelete(NULL);
	}
	gui_state_init();
	gui_screen_init();
	gui_add_subtasks();
	gui_init_fps();
	
	// Module variables
	req_message_box = false;
	
	// Set the initially displayed screen
	gui_set_screen(GUI_SCREEN_MAIN);
	
	while (1) {
		// This task runs every GUI_EVAL_MSEC mSec
		vTaskDelay(pdMS_TO_TICKS(GUI_EVAL_MSEC));
		lv_task_handler();
	}
}


/**
 * Set the currently displayed screen
 */
void gui_set_screen(int n)
{
	if (n < GUI_NUM_SCREENS) {
		if ((gui_cur_screen_index != GUI_SCREEN_MAIN) && (n == GUI_SCREEN_MAIN)) {
			if (task_handle_lep != NULL) {
				xTaskNotify(task_handle_lep, LEP_NOTIFY_EN_GUI_FRAME_MASK, eSetBits);
			}
		}
		if ((gui_cur_screen_index == GUI_SCREEN_MAIN) && (n != GUI_SCREEN_MAIN)) {
			if (task_handle_lep != NULL) {
				xTaskNotify(task_handle_lep, LEP_NOTIFY_DIS_GUI_FRAME_MASK, eSetBits);
			}
		}
	
		gui_cur_screen_index = n;
		
		gui_screen_main_set_active(n == GUI_SCREEN_MAIN);
		gui_screen_settings_set_active(n == GUI_SCREEN_SETTINGS);
		gui_screen_num_entry_set_active(n == GUI_SCREEN_NUM_ENTRY);
		gui_screen_emissivity_set_active(n == GUI_SCREEN_EMISSIVITY);
		gui_screen_info_set_active(n == GUI_SCREEN_INFO);
		gui_screen_network_set_active(n == GUI_SCREEN_NETWORK);
		gui_screen_time_set_active(n == GUI_SCREEN_TIME);
		gui_screen_wifi_set_active(n == GUI_SCREEN_WIFI);
		gui_screen_view_set_active(n == GUI_SCREEN_VIEW);
		gui_screen_browse_set_active(n == GUI_SCREEN_BROWSE);
		gui_screen_update_set_active(n == GUI_SCREEN_UPDATE);
		
		lv_scr_load(gui_screens[n]);
	}
}


/**
 * Set the filename of the last image recorded for us to display when notified
 */
void gui_set_write_filename(char* name)
{
	char c;
	int i = 0;
	int n;
	
	n = sizeof(record_filename);
	c = *name;
	while ((i < (n-1)) && (c != 0)) {
		record_filename[i++] = c;
		c = *(name + i);
	}
	record_filename[i] = 0; // terminate
}


/**
 * Set the btn pressed in a messagebox - used to trigger activity in response
 * to specific buttons
 */
void gui_set_msgbox_btn(uint16_t btn)
{
	if (fw_req_upd_message_box) {
		// Special case for messagebox requesting user if they want to perform a FW
		// update which can occur in any screen
		if (btn == GUI_MSG_BOX_BTN_AFFIRM) {
			// User wants to update FW - let rsp_task know so it can try to start the update
			xTaskNotify(task_handle_rsp, RSP_NOTIFY_FW_UPD_EN_MASK, eSetBits);
		}
		fw_req_upd_message_box = false;
	} else {
		// Call screens that want to know which button
		switch (gui_cur_screen_index) {
			case GUI_SCREEN_BROWSE:
				gui_screen_browse_set_msgbox_btn(btn);
				break;
			
			case GUI_SCREEN_VIEW:
				gui_screen_view_set_msgbox_btn(btn);
				break;
			
			case GUI_SCREEN_UPDATE:
				gui_screen_update_set_msgbox_btn(btn);
				break;
				
			case GUI_SCREEN_INFO:
				gui_screen_info_set_msgbox_btn(btn);
				break;
		}
	}
}


/**
 * Set a timestamp value to pass on to gui_screen_view as part of a video playback
 */
void gui_set_playback_ts(uint32_t ts)
{
	video_ts = ts;
}



//
// GUI Task Internal functions
//

/**
 * Initialize the LittleVGL system including initializing the LCD display and
 * Touchscreen controller.
 */
static bool gui_lvgl_init()
{
	// Initialize lvgl
	lv_init();
	
	//
	// Interface and driver initialization
	//
	disp_driver_init(true);
	touch_driver_init();
	
	// Install the display driver
	lv_disp_buf_init(&lvgl_disp_buf, lvgl_disp_buf1, lvgl_disp_buf2, LVGL_DISP_BUF_SIZE);
	lv_disp_drv_init(&lvgl_disp_drv);
	lvgl_disp_drv.flush_cb = disp_driver_flush;
	lvgl_disp_drv.buffer = &lvgl_disp_buf;
	lv_disp_drv_register(&lvgl_disp_drv);
	
	// Install the touchscreen driver
    lv_indev_drv_init(&lvgl_indev_drv);
    lvgl_indev_drv.read_cb = touch_driver_read;
    lvgl_indev_drv.type = LV_INDEV_TYPE_POINTER;
    lv_indev_drv_register(&lvgl_indev_drv);
    
    // Hook LittleVGL's timebase to its CPU system tick so it can keep track of time
    esp_register_freertos_tick_hook(lv_tick_callback);
    
    return true;
}



/**
 * Initialize the screen objects and their control callbacks
 */
static void gui_screen_init()
{
	// Initialize the screens
	gui_screens[GUI_SCREEN_MAIN] = gui_screen_main_create();
	gui_screens[GUI_SCREEN_SETTINGS] = gui_screen_settings_create();
	gui_screens[GUI_SCREEN_NUM_ENTRY] = gui_screen_num_entry_create();
	gui_screens[GUI_SCREEN_EMISSIVITY] = gui_screen_emissivity_create();
	gui_screens[GUI_SCREEN_INFO] = gui_screen_info_create();
	gui_screens[GUI_SCREEN_NETWORK] = gui_screen_network_create();
	gui_screens[GUI_SCREEN_TIME] = gui_screen_time_create();
	gui_screens[GUI_SCREEN_WIFI] = gui_screen_wifi_create();
	gui_screens[GUI_SCREEN_VIEW] = gui_screen_view_create();
	gui_screens[GUI_SCREEN_BROWSE] = gui_screen_browse_create();
	gui_screens[GUI_SCREEN_UPDATE] = gui_screen_update_create();
}


/**
 * Add the LittleVGL sub-tasks and specify their evaluation period
 */
static void gui_add_subtasks()
{
	// Event handler sub-task runs every GUI_EVAL_MSEC mSec
	lvgl_tasks[LVGL_ST_EVENT] = lv_task_create(gui_task_event_handler_task, GUI_EVAL_MSEC,
		LV_TASK_PRIO_MID, NULL);
		
	// Message box display sub-task runs every GUI_EVAL_MSEC mSec
	lvgl_tasks[LVGL_ST_MESSAGEBOX] = lv_task_create(gui_task_messagebox_handler_task, GUI_EVAL_MSEC,
		LV_TASK_PRIO_LOW, NULL);
}
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
