danjulio/tCam/tCam-Mini/firmware/components/lepton/lepton_utilities.c

/*
 * Lepton related utilities
 *
 * Contains utility and access functions for the Lepton.
 *
 * Note: I noticed that on occasion, the first time some commands run on the lepton
 * will fail either silently or with an error response code.  The access routines in
 * this module attempt to detect and retry the commands if necessary.
 *
 * Copyright 2020 Dan Julio
 *
 * This file is part of tCam.
 *
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
 */
#include "lepton_utilities.h"
#include "cci.h"
#include "i2c.h"
#include "esp_system.h"
#include "esp_log.h"
#include "sys_utilities.h"
#include "vospi.h"
#include "system_config.h"
#include <string.h>



//
// Lepton Utilities variables
//
static const char* TAG = "lepton_utilities";

static bool lep_is_radiometric = false;
static int lep_type;



//
// Lepton Utilities API
//

bool lepton_init()
{
	char pn[33];
	uint32_t val, rsp;
	json_config_t* lep_stP = system_get_lep_st();
  
  	// Attempt to ping the Lepton to validate communication
  	// If this is successful, we assume further communication will be successful
  	rsp = cci_run_ping();
  	if (rsp != 0) {
  		ESP_LOGE(TAG, "Lepton communication failed (%d)", rsp);
  		return false;
	}
	
	// Get the Lepton type (part number) to determine if it's a Lepton 3.0, 3.1 or 3.5
	cci_get_part_number(pn);
	ESP_LOGI(TAG, "Found Lepton, part number: %s", pn);
	if (strncmp(pn, "500-0771", 8) == 0) {
		ESP_LOGI(TAG, "  Radiometric Lepton 3.5");
		lep_is_radiometric = true;
		lep_type = LEP_TYPE_3_5;
	} else if (strncmp(pn, "500-0758", 8) == 0) {
		ESP_LOGI(TAG, "  Radiometric Lepton 3.1");
		lep_is_radiometric = true;
		lep_type = LEP_TYPE_3_1;
	} else if (strncmp(pn, "500-0726", 8) == 0) {
		ESP_LOGI(TAG, "  Non-radiometric Lepton 3.0");
		lep_is_radiometric = false;
		lep_type = LEP_TYPE_3_0;
	} else {
		ESP_LOGI(TAG, "  Unsupported Lepton");
		lep_is_radiometric = true;
		lep_type = LEP_TYPE_UNK;
	}
	
	if (lep_is_radiometric) {
		// Configure Radiometry for TLinear enabled, auto-resolution
		cci_set_radiometry_enable_state(CCI_RADIOMETRY_ENABLED);
		rsp = cci_get_radiometry_enable_state();
		ESP_LOGI(TAG, "Lepton Radiometry = %d", rsp);
		if (rsp != CCI_RADIOMETRY_ENABLED) {
			// Make one more effort
			vTaskDelay(pdMS_TO_TICKS(10));
			ESP_LOGI(TAG, "Retry Set Lepton Radiometry");
			cci_set_radiometry_enable_state(CCI_RADIOMETRY_ENABLED);
			rsp = cci_get_radiometry_enable_state();
			ESP_LOGI(TAG, "Lepton Radiometry = %d", rsp);
			if (rsp != CCI_RADIOMETRY_ENABLED) {
				ESP_LOGE(TAG, "Lepton communication failed (%d)", rsp);
				return false;
			}
		}
	
		// TLinear depends on AGC
		val = (lep_stP->agc_set_enabled) ? CCI_RADIOMETRY_TLINEAR_DISABLED : CCI_RADIOMETRY_TLINEAR_ENABLED;
		cci_set_radiometry_tlinear_enable_state(val);
		rsp = cci_get_radiometry_tlinear_enable_state();
		ESP_LOGI(TAG, "Lepton Radiometry TLinear = %d", rsp);
		if (rsp != val) {
			ESP_LOGE(TAG, "Lepton communication failed (%d)", rsp);
	  		return false;
		}
		
		cci_set_radiometry_tlinear_auto_res(CCI_RADIOMETRY_AUTO_RES_ENABLED);
		rsp = cci_get_radiometry_tlinear_auto_res();
		ESP_LOGI(TAG, "Lepton Radiometry Auto Resolution = %d", rsp);
		if (rsp != CCI_RADIOMETRY_AUTO_RES_ENABLED) {
			ESP_LOGE(TAG, "Lepton communication failed (%d)", rsp);
	  		return false;
		}
	}
	
	// Enable AGC calcs for a smooth transition between modes
	cci_set_agc_calc_enable_state(CCI_AGC_ENABLED);
	rsp = cci_get_agc_calc_enable_state();
	ESP_LOGI(TAG, "Lepton AGC Calcs = %d", rsp);
	if (rsp != CCI_AGC_ENABLED) {
		ESP_LOGE(TAG, "Lepton communication failed (%d)", rsp);
  		return false;
	}
	
	// AGC
	val = (lep_stP->agc_set_enabled) ? CCI_AGC_ENABLED : CCI_AGC_DISABLED;
	cci_set_agc_enable_state(val);
	rsp = cci_get_agc_enable_state();
	ESP_LOGI(TAG, "Lepton AGC = %d", rsp);
	if (rsp != val) {
		ESP_LOGE(TAG, "Lepton communication failed (%d)", rsp);
  		return false;
	}
	
	// Enable telemetry
	cci_set_telemetry_enable_state(CCI_TELEMETRY_ENABLED);
	rsp = cci_get_telemetry_enable_state();
	ESP_LOGI(TAG, "Lepton Telemetry = %d", rsp);
	if (rsp != CCI_TELEMETRY_ENABLED) {
		ESP_LOGE(TAG, "Lepton communication failed (%d)", rsp);
  		return false;
	}
	vospi_include_telem(true);
	
	// GAIN
	switch (lep_stP->gain_mode) {
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
